MAWoodMain/PowerMonitor/Software/src/main/java/org/ladbury/powerMonitor/packets/STM8PacketCollector.java

package org.ladbury.powerMonitor.packets;

import com.pi4j.io.serial.*;

import java.io.IOException;
import java.time.Instant;
import java.util.*;

public class STM8PacketCollector extends Thread implements SerialDataEventListener, PacketCollector
{
    private static final byte[] START_SEQUENCE;
    private static final int PACKET_LENGTH;
    private final List<Byte> incomingBytes;
    private List<Byte> bytes;

    private final Collection<PacketEventListener> listeners;

    private long extractionPeriod;

    private final Serial serial;
    private final SerialConfig config;

    static
    {
        final char[] startString = "PM_START".toCharArray();
        START_SEQUENCE = new byte[startString.length];
        for (int i = 0; i < startString.length; i++)
            START_SEQUENCE[i] = (byte)startString[i];
        PACKET_LENGTH = START_SEQUENCE.length+10+1+9*2*10;
    }

    public STM8PacketCollector(long extractionPeriod)
    {
        this.extractionPeriod = extractionPeriod;
        this.bytes = new ArrayList<>();
        this.incomingBytes = new ArrayList<>();
        this.listeners = new ArrayList<>();
        this.serial = SerialFactory.createInstance();

        config = new SerialConfig();
        config.device("/dev/ttyS0") //config.device(SerialPort.getDefaultPort()) /dev/ttyAMA0 didn't work
                .baud(Baud._230400)
                .dataBits(DataBits._8)
                .stopBits(StopBits._1)
                .parity(Parity.NONE)
                .flowControl(FlowControl.NONE);
        serial.addListener(this);
    }
    @Override
    public void run()
    {
        long time;
        List<Packet> newPackets = new ArrayList<>();
        super.run();
        try {
            serial.open(config);
        } catch (IOException e) {
            e.printStackTrace();
            System.exit(5);
        }

        while(!Thread.interrupted())
        {
            //process list of serial bytes accumulated for period
            time = System.currentTimeMillis();

            try {
                if(incomingBytes.size() > 0)
                {
                    synchronized (incomingBytes)
                    {
                        //System.err.println(incomingBytes.toString()); //debug for log
                        bytes.addAll(incomingBytes);
                        incomingBytes.clear();
                    }
                    newPackets.clear();
                    Instant sampleStart = Instant.now().minusMillis(extractionPeriod);
                    Collection<byte[]> rawPackets = extractPackets(bytes);
                    bytes.clear();
                    for(byte[] packet:rawPackets)
                    {
                        sampleStart = sampleStart.plusMillis(extractionPeriod/rawPackets.size());
                        try
                        {
                            newPackets.add(new Packet(packet, sampleStart)); // full serial packet without start sequence
                        } catch (IllegalArgumentException ignored) {}
                    }
                    alertPacketListeners(newPackets);

                }
            } catch (Exception e) {
                e.printStackTrace();
                if (this.bytes == null) {
                    this.bytes = new ArrayList<>();
                    System.err.println( "Null 'this.bytes' in STM8PacketCollector, recreated");
                }
            }
            //accumulate packets for the period (assume top half of while is short time)
            while(time + extractionPeriod > System.currentTimeMillis())
            {
                // wait half the remaining time
                try
                {
                    Thread.sleep(Math.max(0,((time + extractionPeriod)-System.currentTimeMillis())/2));
                } catch (InterruptedException ignored) {}
            }
        }
    }
    private void alertPacketListeners(Collection<Packet> newPackets)
    {
        for(PacketEventListener listener:listeners) listener.handleNewPackets(newPackets);
    }

    private Collection<byte[]> extractPackets(Collection<Byte> rawData)throws NullPointerException
    {
        Collection<byte[]> packets = new ArrayList<>();
        boolean sequenceValid;
        int dataIdx = 0;

        /* Unbox Byte array to byte array */
        byte[] data = new byte[rawData.size()];
        for(Byte b: rawData)
            if(b!=null) data[dataIdx++] = b;
            else System.err.println( "Null b in STM8PacketCollector");
        /* Reset index */
        dataIdx = 0;

        do {
            /* Matches first char of START_SEQUENCE */
            if(data[dataIdx] == START_SEQUENCE[0])
            {
                /* Look ahead and verify sequence, assume valid until error */
                sequenceValid = true;
                for(int sequenceIdx = 1; sequenceIdx < START_SEQUENCE.length; sequenceIdx++)
                {
                    /* If invalid char found */
                    if(data[dataIdx + sequenceIdx] != START_SEQUENCE[sequenceIdx])
                    {
                        /* If any out of turn character appear reject start sequence match */
                        sequenceValid = false;
                        break;
                    }
                }
                /* If start sequence was validated and there is enough data left to finish a packet */
                if(sequenceValid && ((dataIdx + START_SEQUENCE.length + PACKET_LENGTH) <= data.length))
                {
                    /* Skip past start sequence */
                    dataIdx += START_SEQUENCE.length;
                    /* Copy out the packet */
                    packets.add(Arrays.copyOfRange(data, dataIdx, dataIdx + PACKET_LENGTH));
                    /* Skip the consumed packet */
                    dataIdx += PACKET_LENGTH;
                }
                else if (sequenceValid)
                {
                    /* Partial packet on the end of the raw data, skip to end */
                    dataIdx = data.length;
                }

            }
            /* Always increment to ensure loop concludes */
            dataIdx++;
        }
        while(dataIdx < data.length);

        return packets;
    }

    public void addPacketEventListener(PacketEventListener listener)
    {
        this.listeners.add(listener);
    }

    @Override
    public void dataReceived(SerialDataEvent serialDataEvent)
    {
        try
        {
            for(byte b:serialDataEvent.getBytes()) incomingBytes.add(b);
        } catch (IOException ignored) {}
    }

    public void close() throws IOException
    {
        this.interrupt();
        serial.close();
    }
}
