MAWoodMain/PowerMonitor/Firmware/calcvi.c

#include "calcvi.h"

int startV, sampleV, sampleI[HARDWARE_CHANNEL_NUM];

float Vrms,realPower[HARDWARE_CHANNEL_NUM],Irms[HARDWARE_CHANNEL_NUM],lastFilteredV,filteredV,filteredI,phaseShiftedV;

float offsetV = ADC_COUNTS>>1;
float offsetI = ADC_COUNTS>>1;

double sumVSquared, instP, sumISquared[HARDWARE_CHANNEL_NUM], sumP[HARDWARE_CHANNEL_NUM];

bool lastVCross,checkVCross;



// Modified version of a method from https://github.com/openenergymonitor/EmonLib/blob/master/EmonLib.cpp
// Calculator credits to the openenergymonitor project (https://github.com/openenergymonitor)
// Current clamp and AC/AC voltage source scaling and calibration is done outside of the firmware so that
// different external devices can be used.
void calcVI(const unsigned int crossings)
{
    unsigned int crossCount = 0;
    unsigned int numberOfSamples = 0;
    double VoltsPerCount;
    int i;
	
    //Reset accumulators
    sumVSquared = 0;
	for(i = 0; i < HARDWARE_CHANNEL_NUM; i++)
	{
		sumISquared[i] = 0;
		sumP[i] = 0;
	}

    //-------------------------------------------------------------------------------------------------------------------------
    // 1) Waits for the waveform to be close to 'zero' (mid-scale adc) part in sin curve.
    //-------------------------------------------------------------------------------------------------------------------------
	do
	{
		startV = readChannel(VOLTAGE_CHANNEL);
		// keep trying until voltage is within 5% of a crossing point (offset zero)
	} while (!((startV<(ADC_COUNTS*0.55))&&(startV>(ADC_COUNTS*0.45))));

     //-------------------------------------------------------------------------------------------------------------------------
     // 2) Main measurement loop
     //-------------------------------------------------------------------------------------------------------------------------
	while(crossCount < crossings)
	{
        numberOfSamples++;
        //-----------------------------------------------------------------------------
        // A) Read in raw voltage and current samples
        //-----------------------------------------------------------------------------

        // read voltage ADC
        sampleV = readChannel(VOLTAGE_CHANNEL);
        // read current ADCs
		for(i = 0; i < HARDWARE_CHANNEL_NUM; i++)
			sampleI[i] = readChannel(CHANNELS[i]);

        lastFilteredV = filteredV;

        //-----------------------------------------------------------------------------
        // B) Apply digital low pass filters to extract the 2.5 V or 1.65 V dc offset,
        //     then subtract this - signal is now centred on 0 counts.
        //-----------------------------------------------------------------------------

        // Voltage part
        offsetV = offsetV + ((sampleV-offsetV)/1024);
        filteredV = sampleV - offsetV;


        //-----------------------------------------------------------------------------
        // C) Root-mean-square method voltage
        //-----------------------------------------------------------------------------

        sumVSquared += filteredV * filteredV;

        //-----------------------------------------------------------------------------
        // E) Phase calibration
        //-----------------------------------------------------------------------------
        phaseShiftedV = lastFilteredV + PHASECAL * (filteredV - lastFilteredV);
		
		for(i = 0; i < HARDWARE_CHANNEL_NUM; i++)
		{
            //-----------------------------------------------------------------------------
            // B) Apply digital low pass filters to extract the 2.5 V or 1.65 V dc offset,
            //     then subtract this - signal is now centred on 0 counts.
            //-----------------------------------------------------------------------------

            // Current part
			offsetI = offsetI + ((sampleI[i]-offsetI)/1024);
			filteredI = sampleI[i] - offsetI;

			//-----------------------------------------------------------------------------
            // D) Root-mean-square method current
            //-----------------------------------------------------------------------------
			sumISquared[i] += filteredI * filteredI;

            //-----------------------------------------------------------------------------
            // F) Instantaneous power calc
            //-----------------------------------------------------------------------------
			instP = phaseShiftedV * filteredI;
			sumP[i] +=instP;
		}
        //-----------------------------------------------------------------------------
        // G) Find the number of times the voltage has crossed the initial voltage
        //    - every 2 crosses we will have sampled 1 wavelength
        //    - so this method allows us to sample an integer number of half wavelengths which increases accuracy
        //-----------------------------------------------------------------------------
        lastVCross = checkVCross;
		checkVCross = sampleV > startV;
        if (numberOfSamples==1) lastVCross = checkVCross;
        if (lastVCross != checkVCross) crossCount++;
    }
    //-------------------------------------------------------------------------------------------------------------------------
    // 3) Post loop calculations
    //-------------------------------------------------------------------------------------------------------------------------
    //Calculation of the root of the mean of the voltage and current squared (rms)
    //Calibration coefficients applied.

    //GJW stuff missing here
	VoltsPerCount = VCC / ADC_COUNTS; //constant 3.3/4096
    Vrms = VoltsPerCount * sqrt(sumVSquared / numberOfSamples);

	for(i = 0; i < HARDWARE_CHANNEL_NUM; i++)
	{
		Irms[i] = VoltsPerCount * sqrt(sumISquared[i] / numberOfSamples);
		// VoltsPerCount applies to current and voltage in power as P=VI
		realPower[i] = VoltsPerCount * VoltsPerCount * sumP[i] / numberOfSamples;
	}

}

float getRealPower(unsigned int channelNo)
{
	return realPower[channelNo];
}

float getIrms(unsigned int channelNo)
{
	return Irms[channelNo];
}

float getVrms()
{
	return Vrms;
}
